KarlK90/yaemk-split-kb/docs/images/6_yaemk_close_up_plain_front.webp

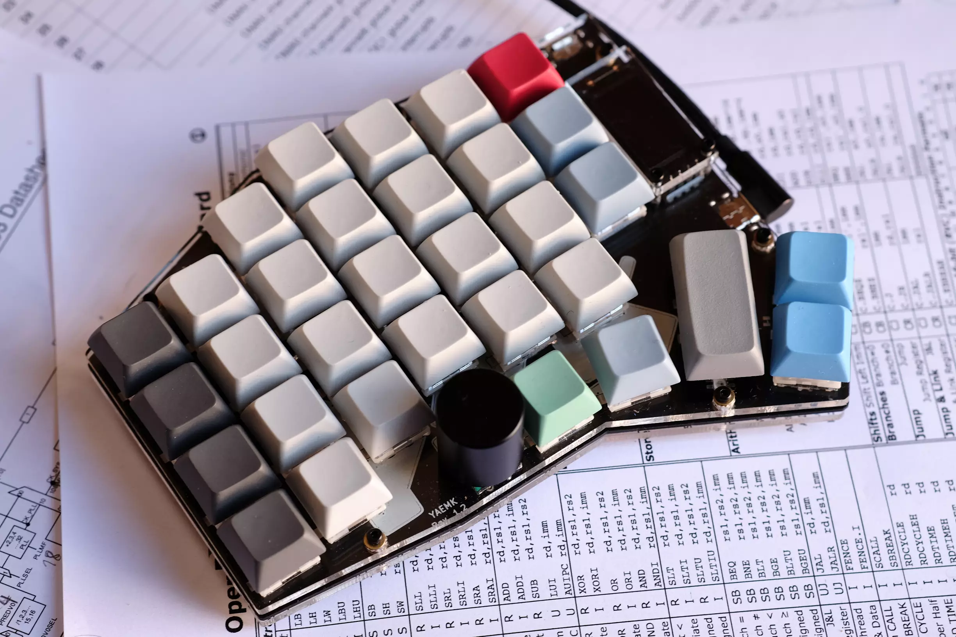
docs/images/6_yaemk_close_up_plain_front.webp
