KarlK90/yaemk-split-kb/docs/images/IMG_20210808_134641-01.jpeg

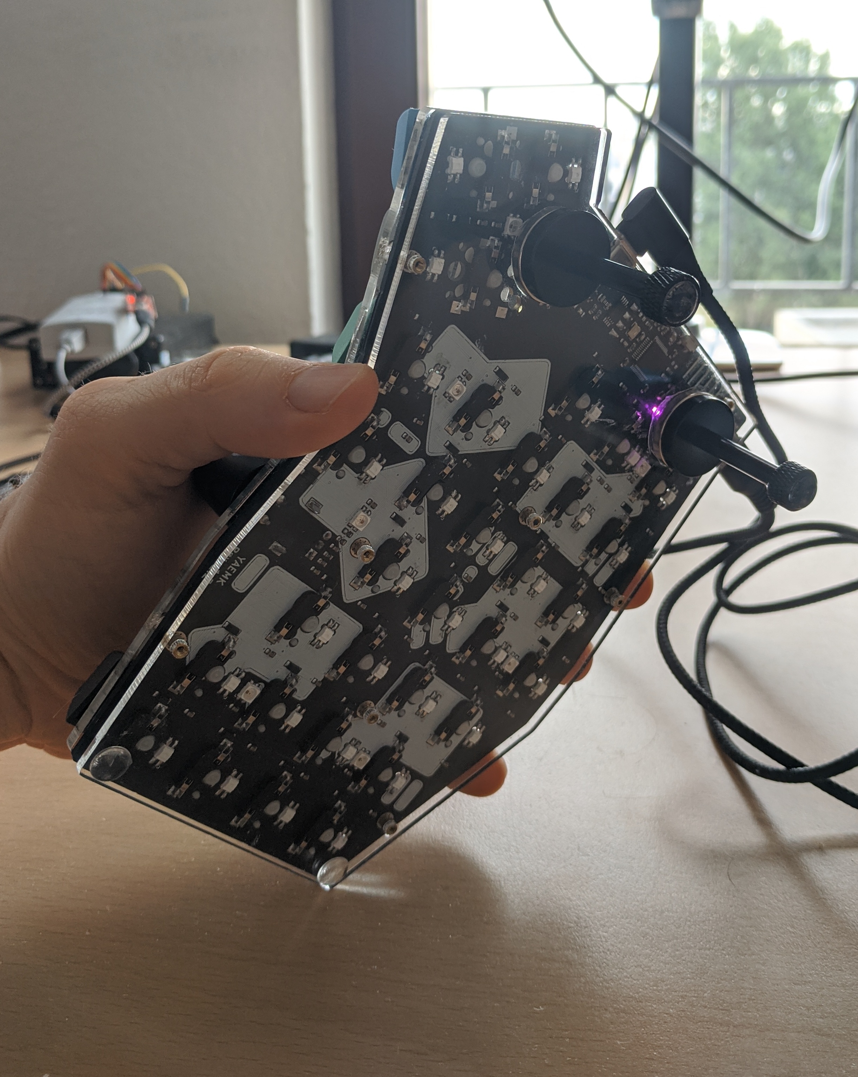
docs/images/IMG_20210808_134641-01.jpeg
