KarlK90/yaemk-split-kb/docs/images/IMG_20210808_134731-01.jpeg

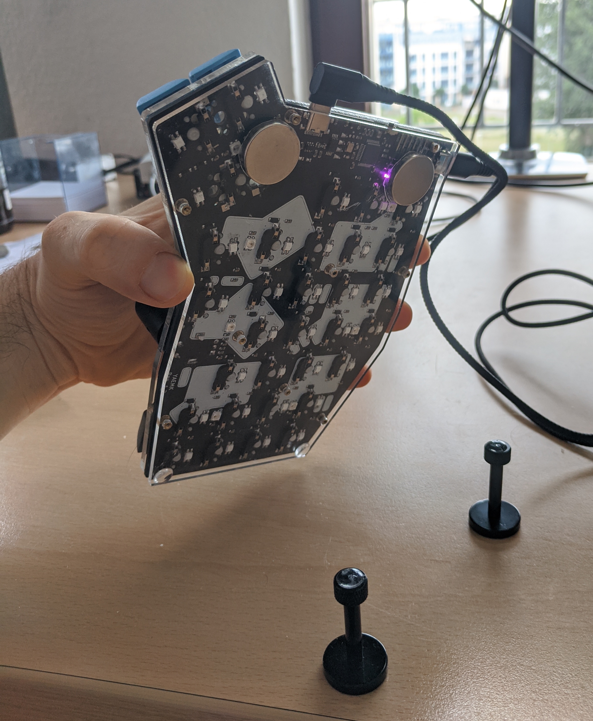
docs/images/IMG_20210808_134731-01.jpeg
